travisbmartin/Iron-Man-HoA/Pi Pico Code/arc_reactor_2.bmp

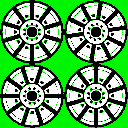
Pi Pico Code/arc_reactor_2.bmp
