travisbmartin/Iron-Man-HoA/Pictures/20240726_164552.jpg

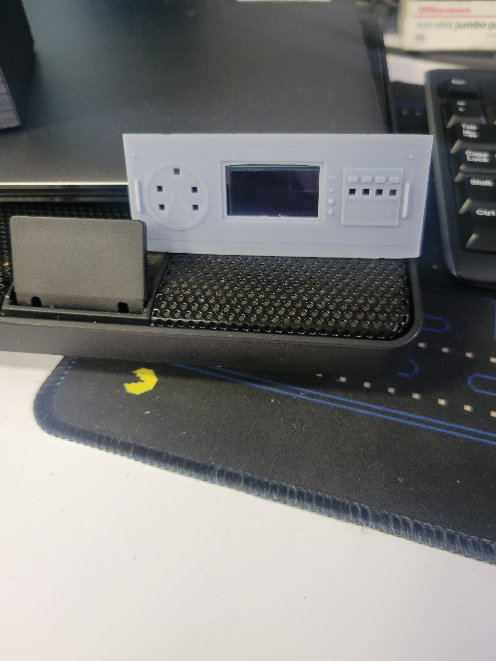
Pictures/20240726_164552.jpg
