travisbmartin/Iron-Man-HoA/Pictures/20240803_234528.jpg

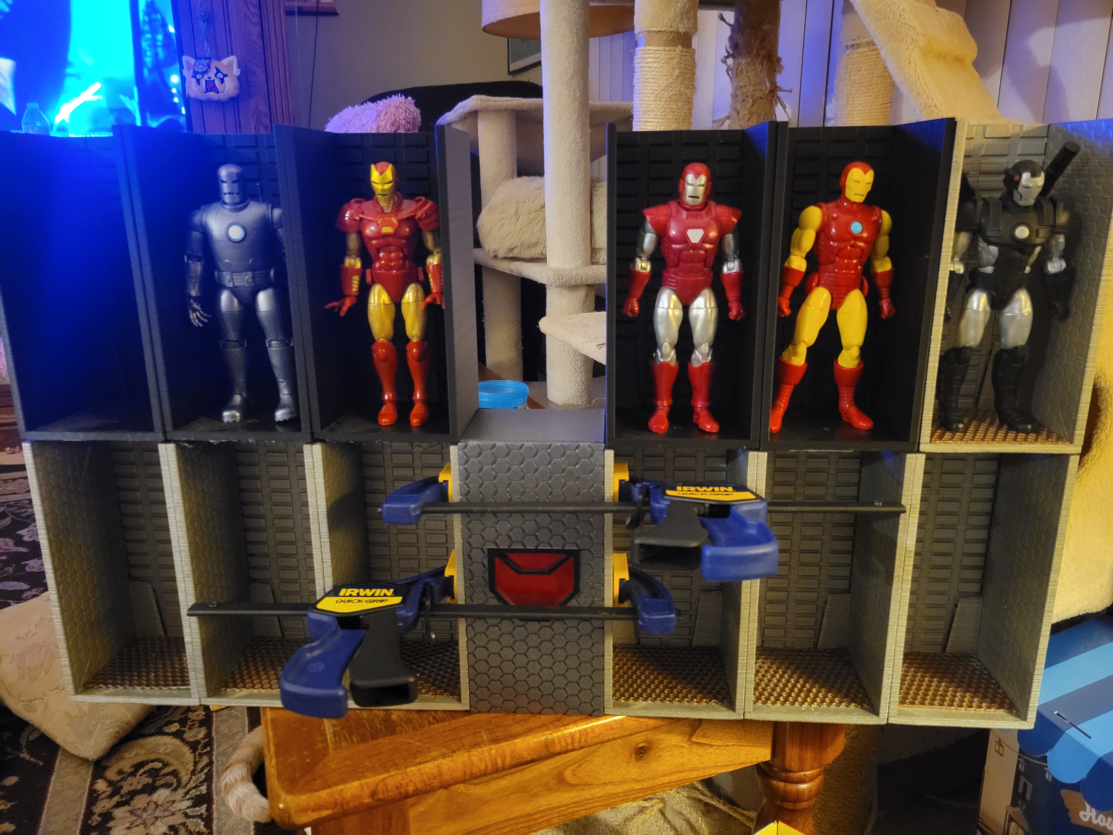
Pictures/20240803_234528.jpg
