travisbmartin/Iron-Man-HoA/Pictures/20240916_043722.jpg

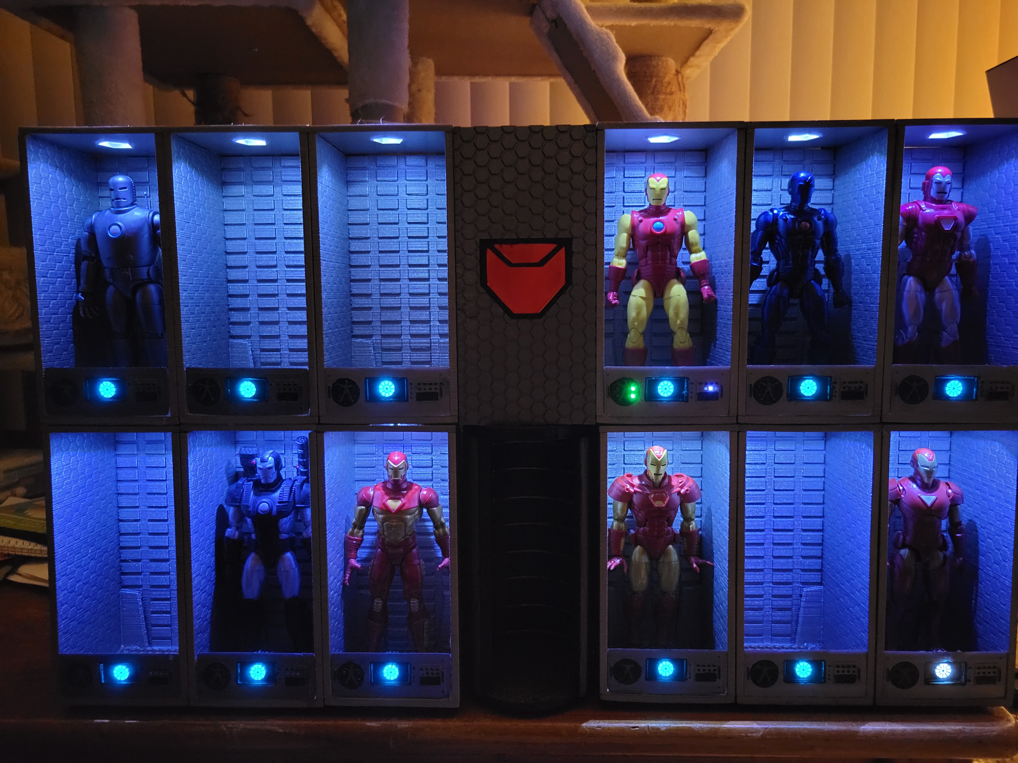
Pictures/20240916_043722.jpg
