travisbmartin/Iron-Man-HoA/Pictures/20240916_043727.jpg

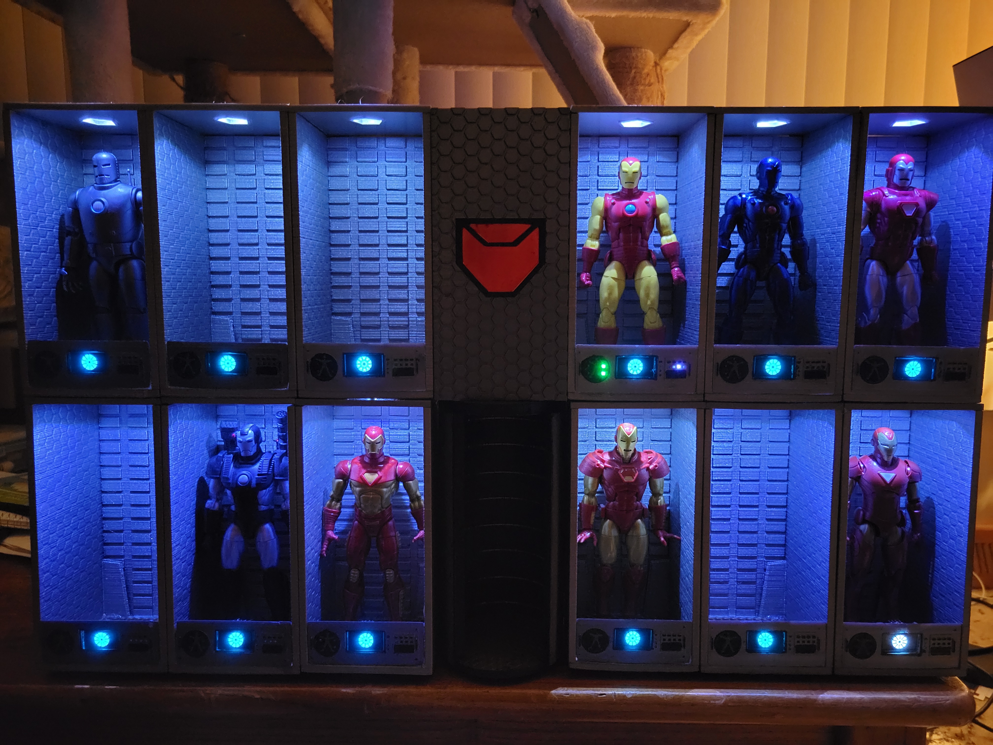
Pictures/20240916_043727.jpg
