travisbmartin/Iron-Man-HoA/Pictures/20240726_163308.jpg

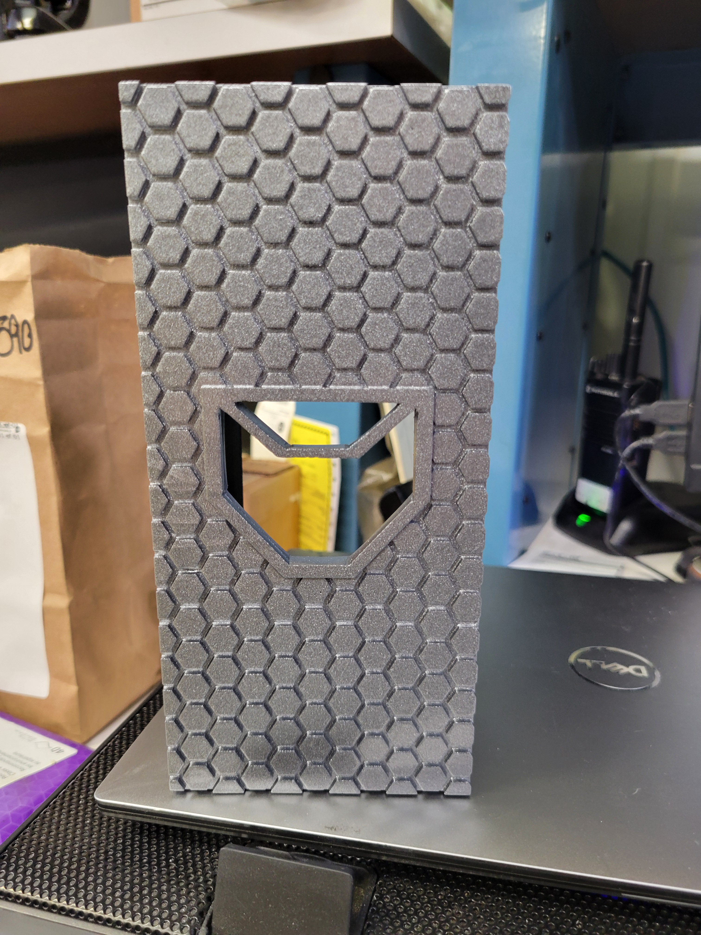
Pictures/20240726_163308.jpg
