travisbmartin/Iron-Man-HoA/Pictures/20240726_163322.jpg

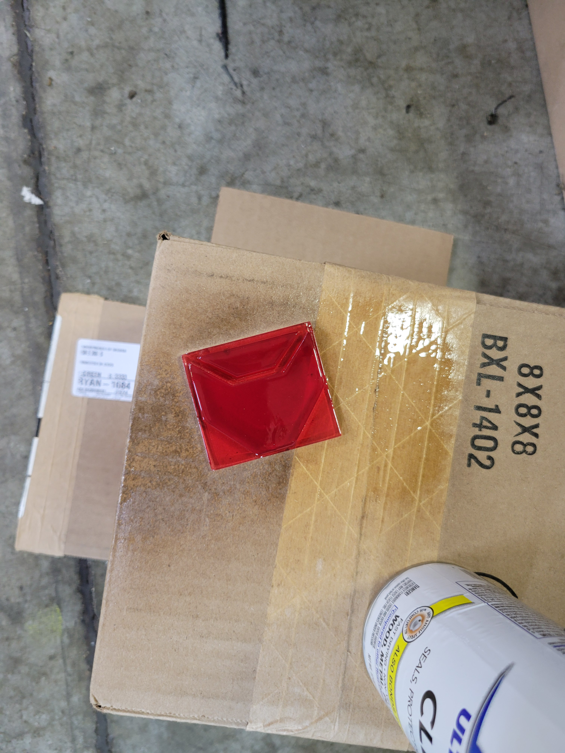
Pictures/20240726_163322.jpg
