travisbmartin/Iron-Man-HoA/Pictures/20240726_164717.jpg

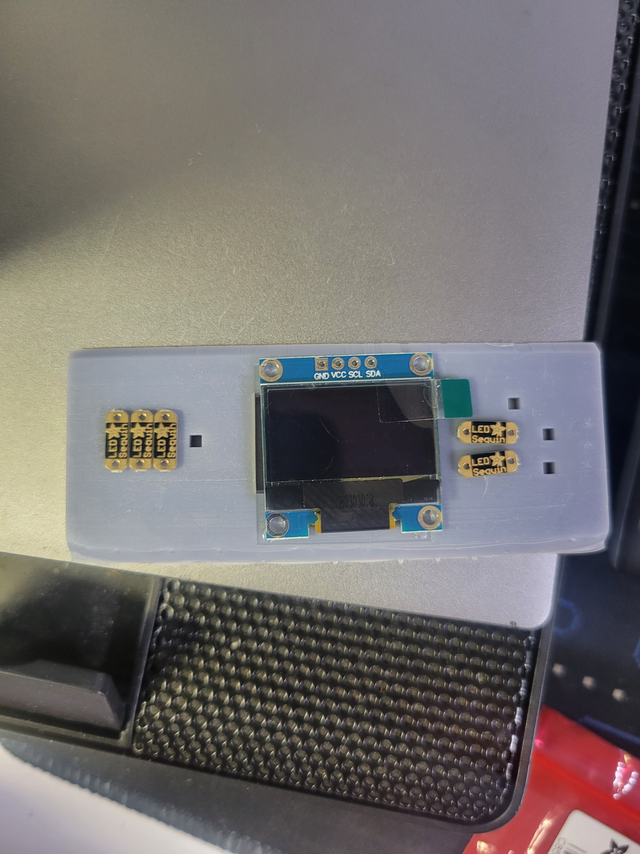
Pictures/20240726_164717.jpg
