travisbmartin/Iron-Man-HoA/Pictures/20240726_182106.jpg

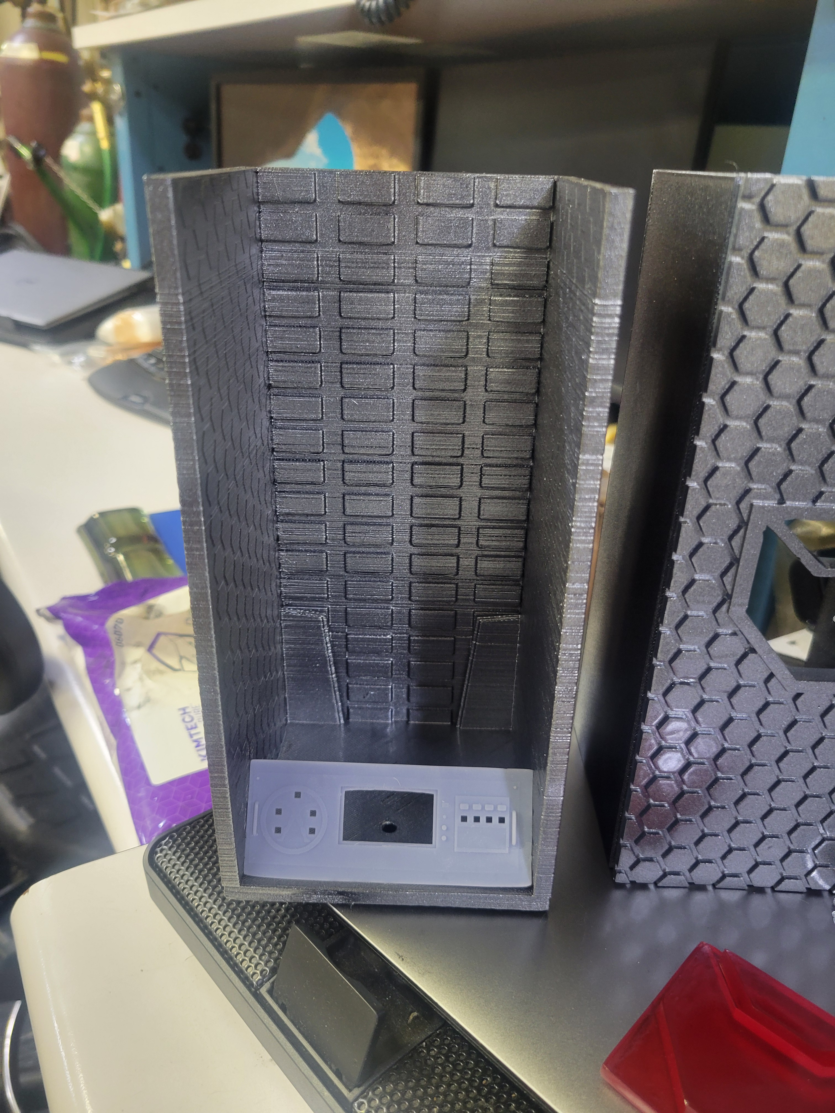
Pictures/20240726_182106.jpg
