travisbmartin/Iron-Man-HoA/Pictures/20240803_234520.jpg

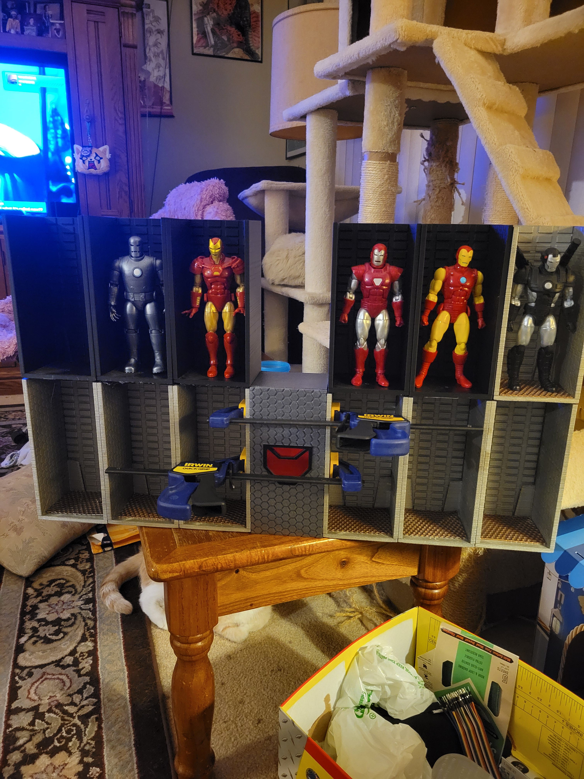
Pictures/20240803_234520.jpg
