travisbmartin/Iron-Man-HoA/Pictures/20240808_183356.jpg

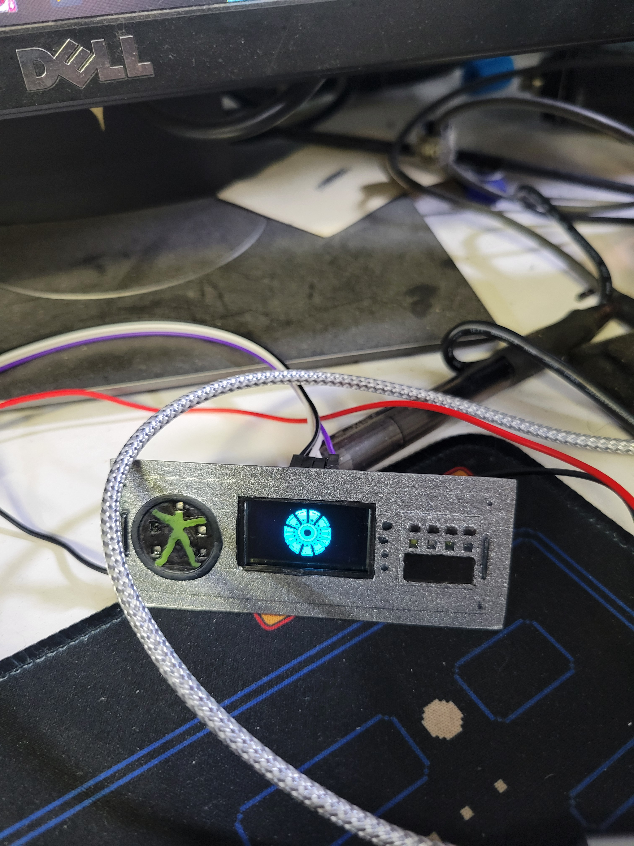
Pictures/20240808_183356.jpg
